JT074084/V1-Bacteria-Killing-Shoe-Display/STL FILES/Door Stuff/V1 FINAL - Door.stl

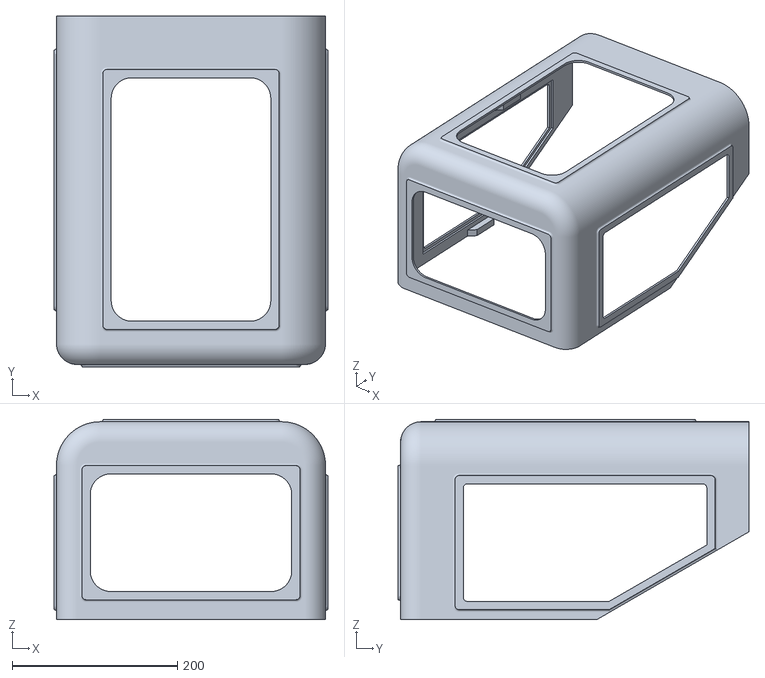
[picture p15: CAD file, 2025-12-03]
STL FILES/Door Stuff/V1 FINAL - Door.stl
331.8 x 425.0 x 242.8
