JT074084/V1-Bacteria-Killing-Shoe-Display/STL FILES/Shoe Bed Stuff/Bed Parts/V1 FINAL - Left Bed - Back.stl

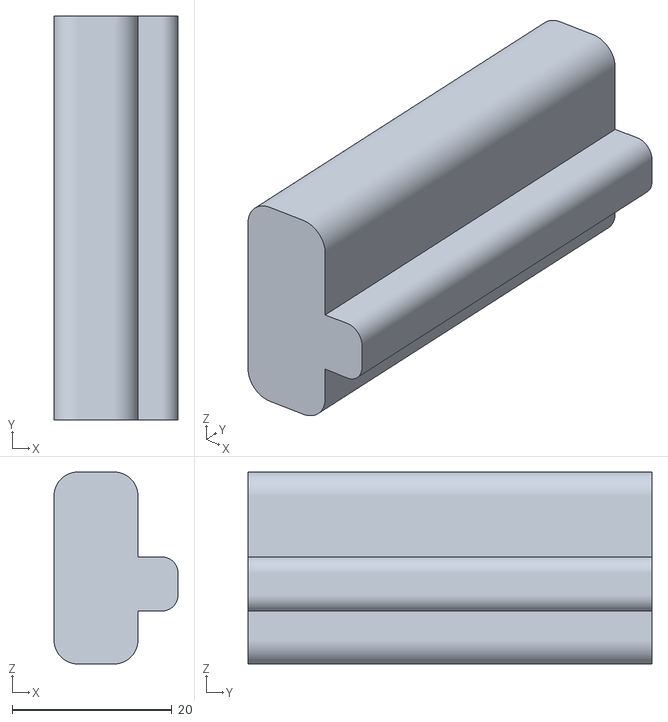
[picture p16: CAD file, 2025-12-03]
STL FILES/Shoe Bed Stuff/Bed Parts/V1 FINAL - Left Bed - Back.stl
15.5 x 50.5 x 24.0
