JT074084/V1-Bacteria-Killing-Shoe-Display/STL FILES/Shoe Bed Stuff/Drag Chain/Wire Chain Bed Connect V1.stl

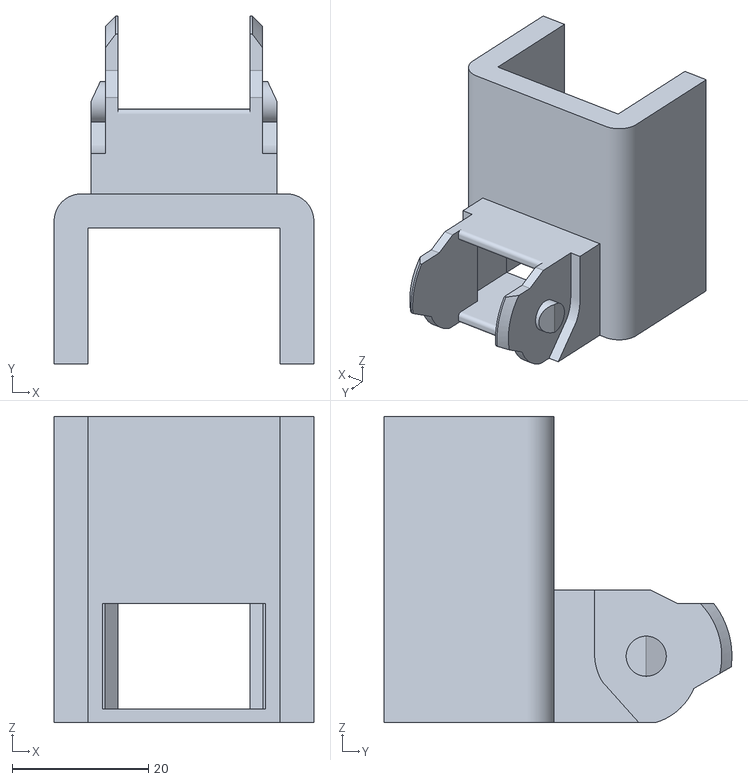
[picture p17: CAD file, 2025-12-03]
STL FILES/Shoe Bed Stuff/Drag Chain/Wire Chain Bed Connect V1.stl
38.2 x 51.1 x 45.0
