JT074084/V1-Bacteria-Killing-Shoe-Display/STL FILES/Shoe Bed Stuff/Logo Cap/V1 FINAL - BPL 2.stl

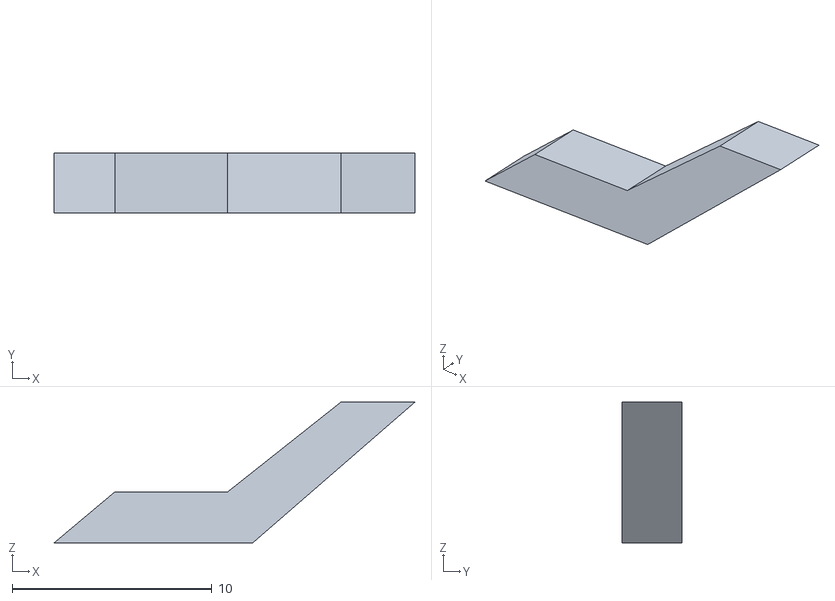
[picture p18: CAD file, 2025-12-03]
STL FILES/Shoe Bed Stuff/Logo Cap/V1 FINAL - BPL 2.stl
18.1 x 3.00 x 7.05
