JT074084/V1-Bacteria-Killing-Shoe-Display/STL FILES/Shoe Bed Stuff/Shoe Sensor and UVC LED Stuff/Shoe Sensor TPU Spring.stl

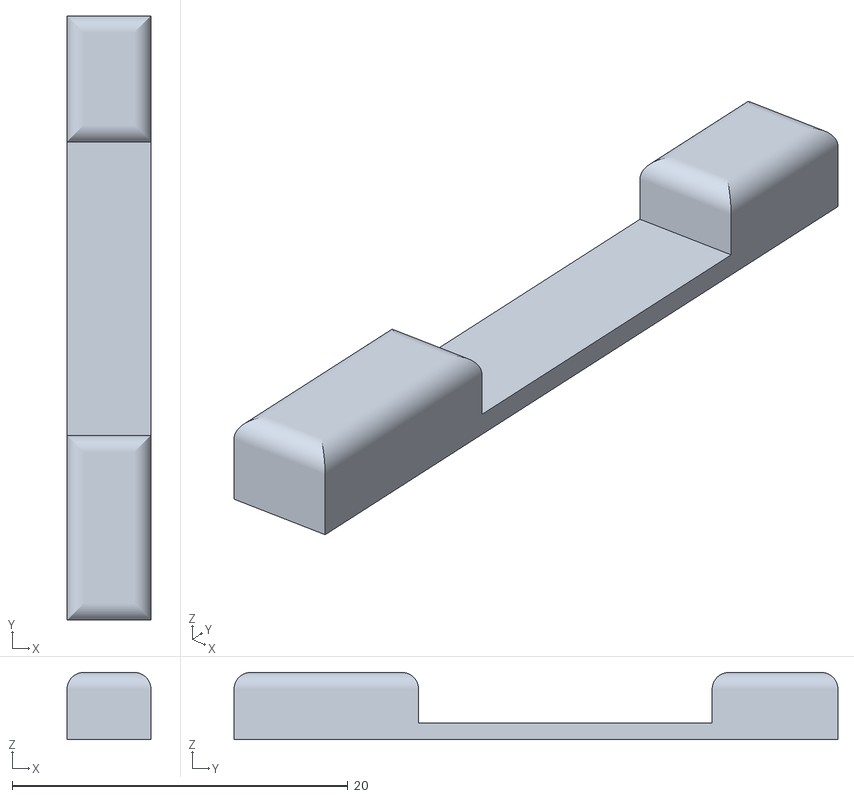
[picture p19: CAD file, 2025-12-03]
STL FILES/Shoe Bed Stuff/Shoe Sensor and UVC LED Stuff/Shoe Sensor TPU Spring.stl
5.00 x 36.0 x 4.00
