JT074084/V1-Bacteria-Killing-Shoe-Display/STL FILES/Shoe Bed Stuff/Shoe Sensor and UVC LED Stuff/UVC LED Stick/UVC LED Stick V1.stl

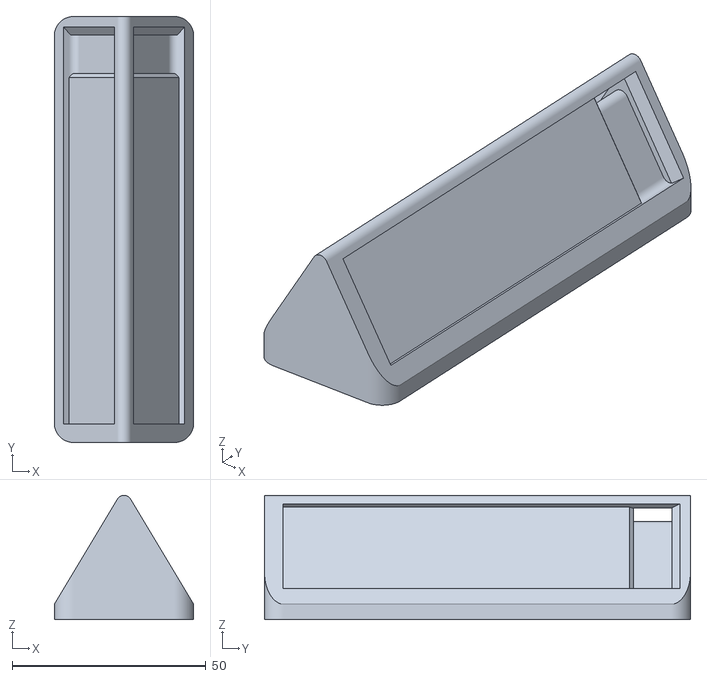
[picture p20: CAD file, 2025-12-03]
STL FILES/Shoe Bed Stuff/Shoe Sensor and UVC LED Stuff/UVC LED Stick/UVC LED Stick V1.stl
36.0 x 110.0 x 32.1
