JT074084/V1-Bacteria-Killing-Shoe-Display/STL FILES/Base Stuff/LED Bar and Base Covers/V1 FINAL - Base Cap.stl

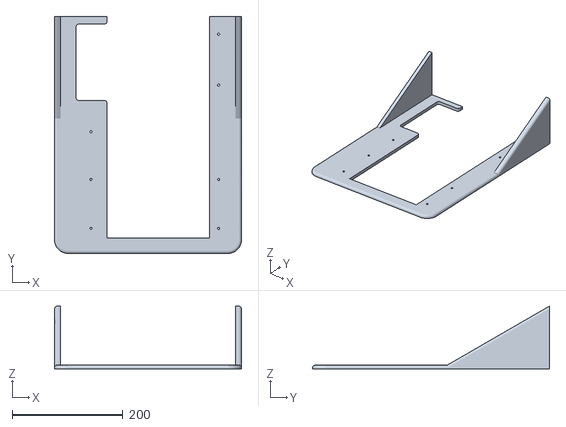
[picture p21: CAD file, 2025-12-03]
STL FILES/Base Stuff/LED Bar and Base Covers/V1 FINAL - Base Cap.stl
337.8 x 428.0 x 113.5
