JT074084/V1-Bacteria-Killing-Shoe-Display/STL FILES/Base Stuff/Left Side Top Half/Left Side Top Half Cap.stl

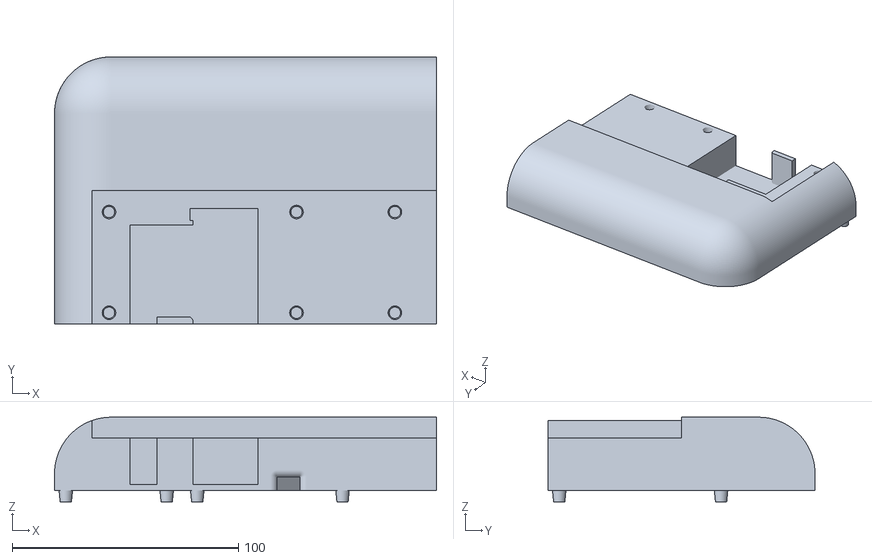
[picture p22: CAD file, 2025-12-03]
STL FILES/Base Stuff/Left Side Top Half/Left Side Top Half Cap.stl
168.9 x 118.1 x 37.4
