JT074084/V1-Bacteria-Killing-Shoe-Display/STL FILES/Base Stuff/Linear Actuator Stuff/Spacers/V1 FINAL - LAS 1.stl

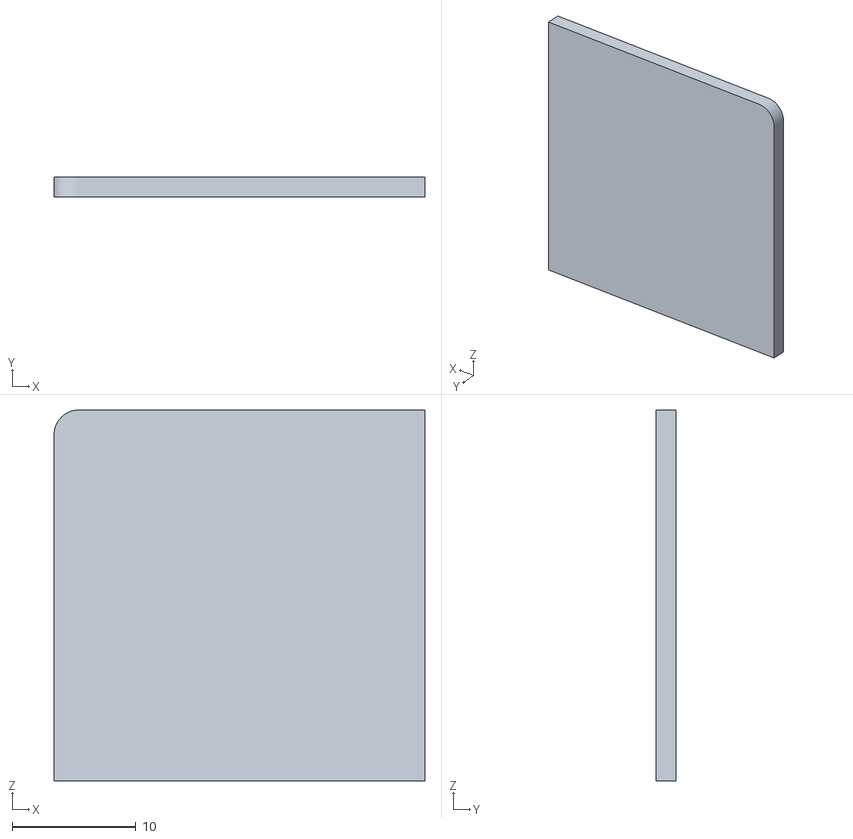
[picture p23: CAD file, 2025-12-03]
STL FILES/Base Stuff/Linear Actuator Stuff/Spacers/V1 FINAL - LAS 1.stl
30.0 x 1.60 x 30.0
