JT074084/V1-Bacteria-Killing-Shoe-Display/STL FILES/Base Stuff/Open:Close Button Stuff/V1 FINAL - Button Spring 2.stl

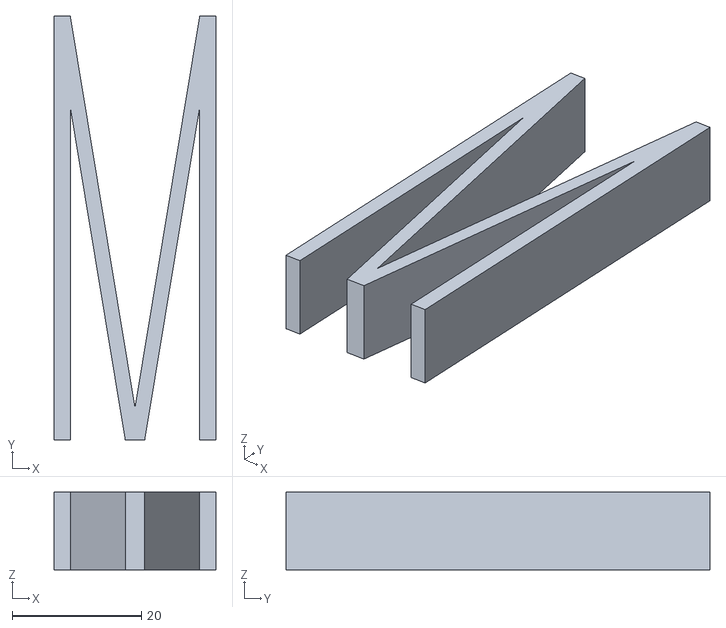
[picture p24: CAD file, 2025-12-03]
STL FILES/Base Stuff/Open:Close Button Stuff/V1 FINAL - Button Spring 2.stl
25.0 x 65.5 x 12.0
