JT074084/V1-Bacteria-Killing-Shoe-Display/STL FILES/Base Stuff/Push Latch Mechanism Side/V1 FINAL - Spring 1.stl

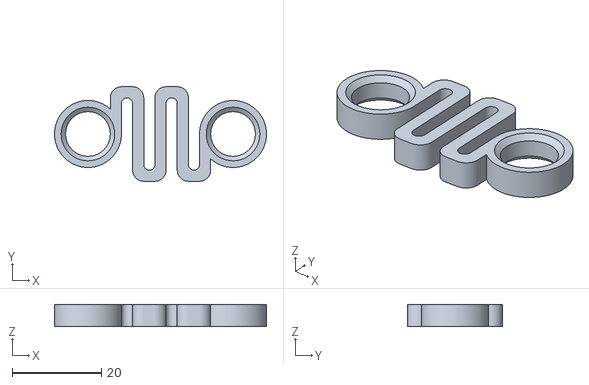
[picture p25: CAD file, 2025-12-03]
STL FILES/Base Stuff/Push Latch Mechanism Side/V1 FINAL - Spring 1.stl
47.5 x 21.2 x 5.00
