JT074084/V1-Bacteria-Killing-Shoe-Display/STL FILES/Base Stuff/Wire Duct Caps/V1 FINAL - Back Wiring Cap 1.stl

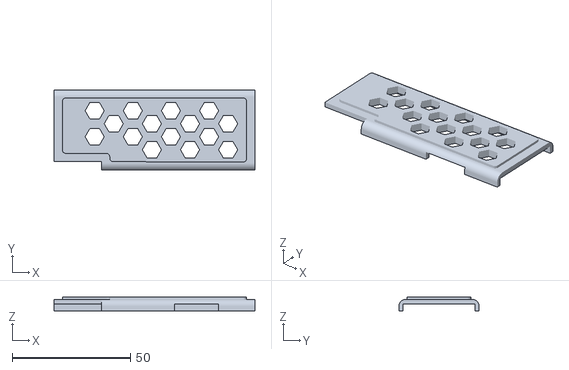
[picture p26: CAD file, 2025-12-03]
STL FILES/Base Stuff/Wire Duct Caps/V1 FINAL - Back Wiring Cap 1.stl
85.0 x 34.0 x 6.00
