JT074084/V1-Bacteria-Killing-Shoe-Display/STL FILES/Door Stuff/Door Arm Stuff/Arm Connecting Pieces/Logo/V1 FINAL - Logo 2.stl

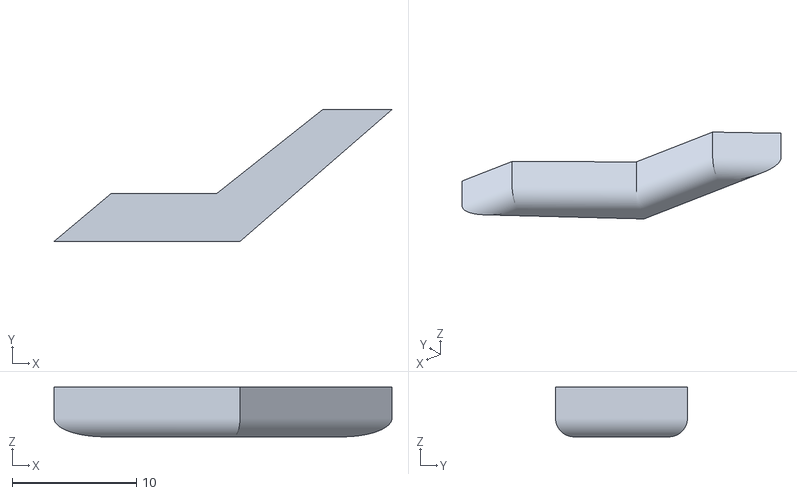
[picture p27: CAD file, 2025-12-03]
STL FILES/Door Stuff/Door Arm Stuff/Arm Connecting Pieces/Logo/V1 FINAL - Logo 2.stl
27.2 x 10.6 x 4.00
