JT074084/V1-Bacteria-Killing-Shoe-Display/STL FILES/Door Stuff/Door Arm Stuff/Arm Connecting Pieces/V1 FINAL - ARM MBB.stl

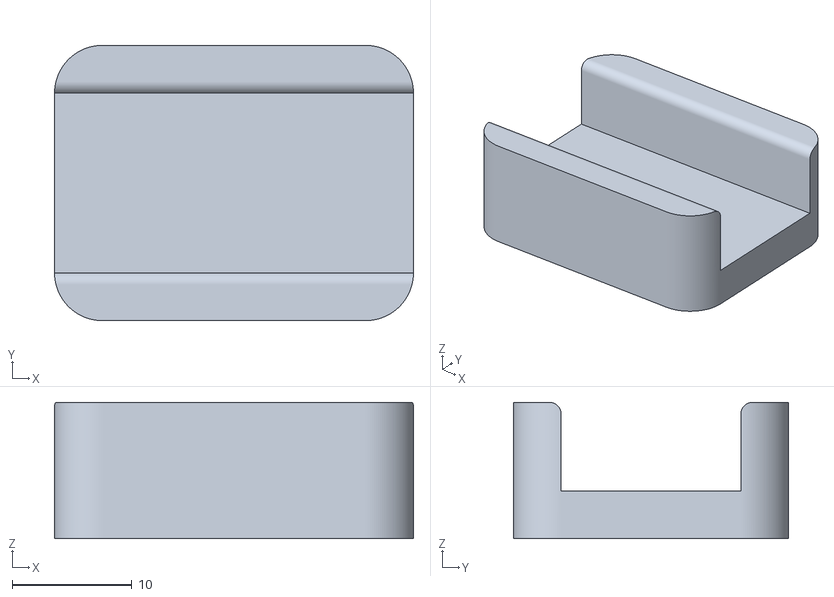
[picture p28: CAD file, 2025-12-03]
STL FILES/Door Stuff/Door Arm Stuff/Arm Connecting Pieces/V1 FINAL - ARM MBB.stl
30.0 x 23.0 x 11.4
