JT074084/V1-Bacteria-Killing-Shoe-Display/STL FILES/Door Stuff/Door Arm Stuff/Right Bearing Case.stl

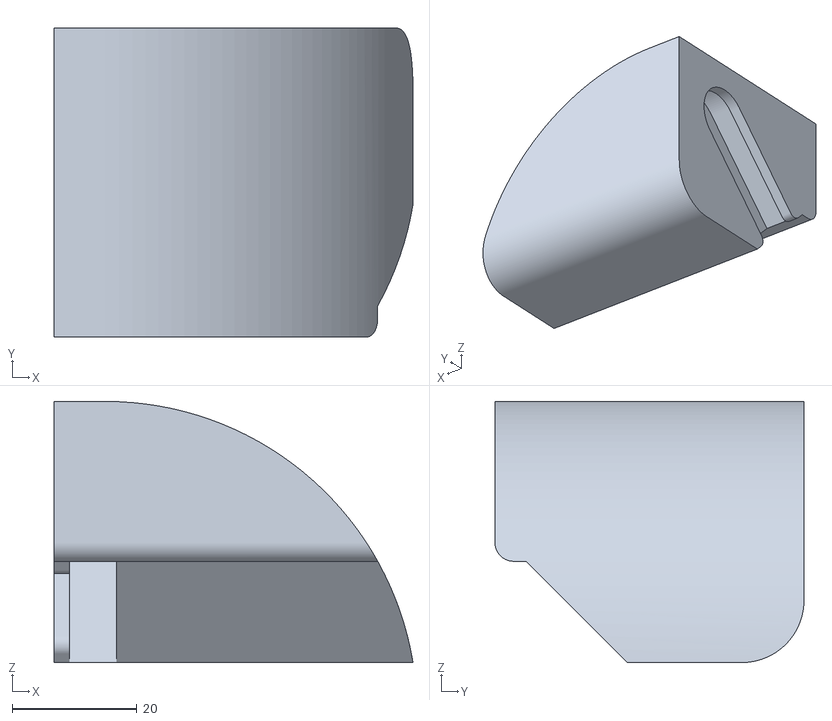
[picture p29: CAD file, 2025-12-03]
STL FILES/Door Stuff/Door Arm Stuff/Right Bearing Case.stl
57.7 x 49.6 x 41.9
