JT074084/V1-Bacteria-Killing-Shoe-Display/STL FILES/Shoe Bed Stuff/Bed Parts/Bed Connect - 2040 Connect.stl

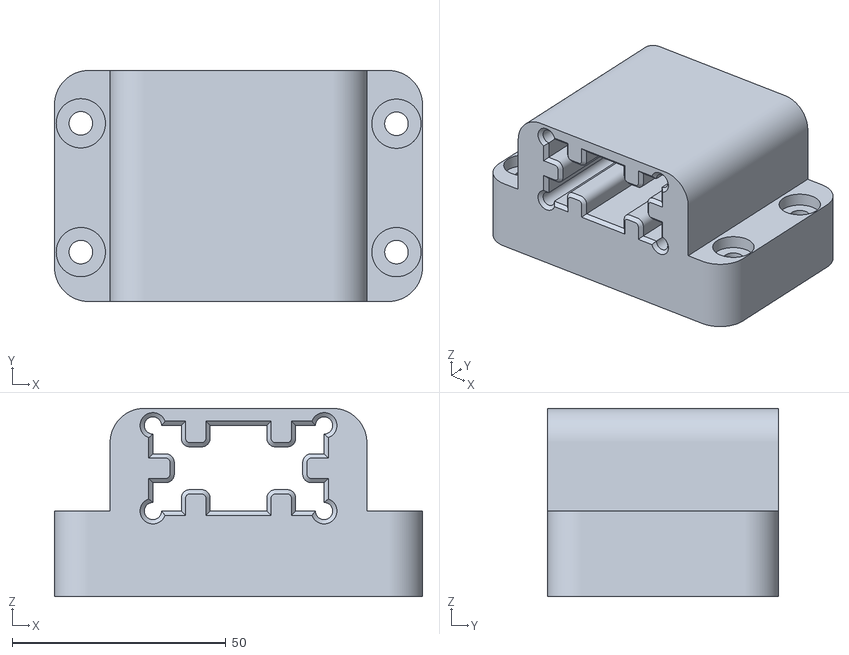
[picture p30: CAD file, 2025-12-03]
STL FILES/Shoe Bed Stuff/Bed Parts/Bed Connect - 2040 Connect.stl
86.0 x 54.0 x 44.0
