JT074084/V1-Bacteria-Killing-Shoe-Display/STL FILES/Shoe Bed Stuff/Drag Chain/chain-segment.stl

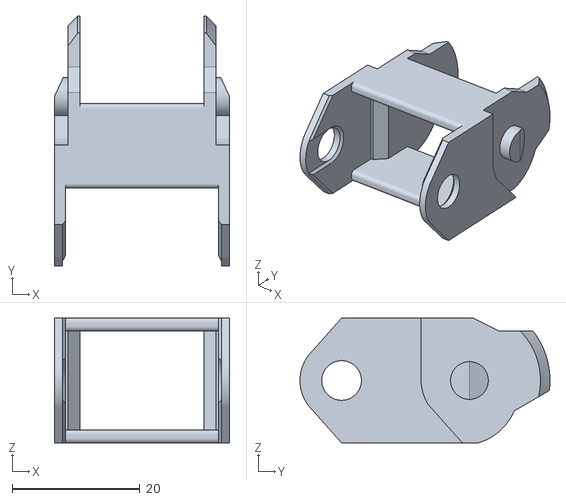
[picture p31: CAD file, 2025-12-03]
STL FILES/Shoe Bed Stuff/Drag Chain/chain-segment.stl
27.4 x 39.1 x 19.5
