JT074084/V1-Bacteria-Killing-Shoe-Display/STL FILES/Shoe Bed Stuff/Logo Cap/V1 FINAL - BPL 3.stl

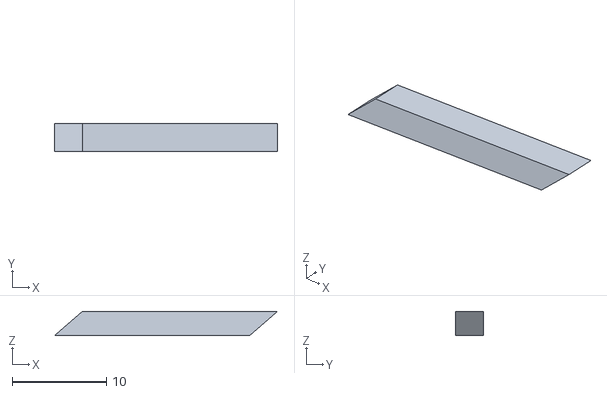
[picture p32: CAD file, 2025-12-03]
STL FILES/Shoe Bed Stuff/Logo Cap/V1 FINAL - BPL 3.stl
23.6 x 3.00 x 2.56
