JT074084/V1-Bacteria-Killing-Shoe-Display/STL FILES/Shoe Bed Stuff/Shoe Sensor and UVC LED Stuff/V1 FINAL - Shoe Sensor.stl

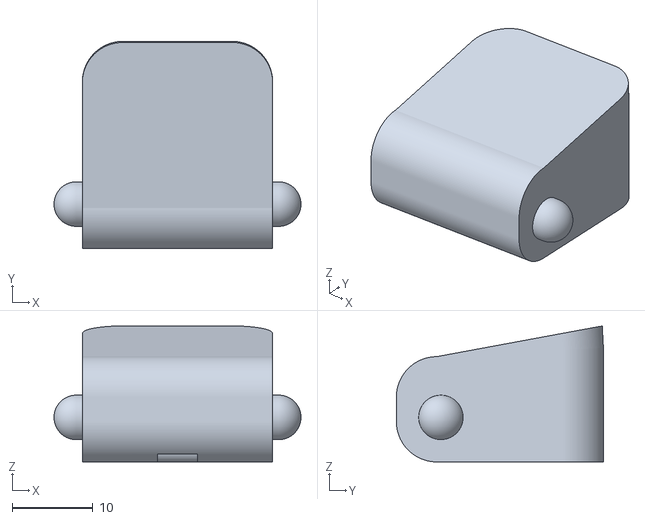
[picture p33: CAD file, 2025-12-03]
STL FILES/Shoe Bed Stuff/Shoe Sensor and UVC LED Stuff/V1 FINAL - Shoe Sensor.stl
30.5 x 25.6 x 16.8
