JT074084/V1-Bacteria-Killing-Shoe-Display/STL FILES/Base Stuff/LED Bar and Base Covers/V1 FINAL - Side LED Attachment.stl

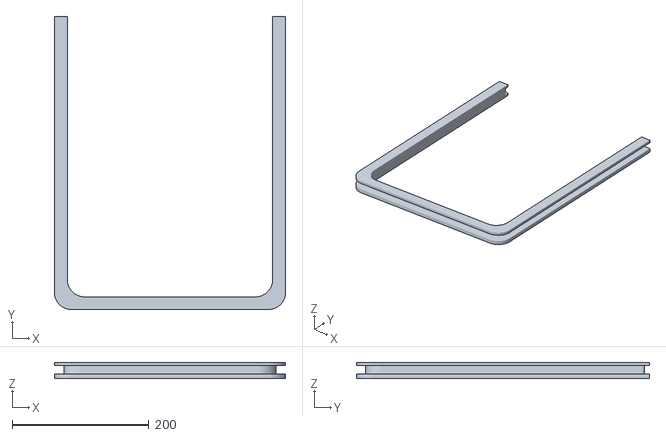
[picture p34: CAD file, 2025-12-03]
STL FILES/Base Stuff/LED Bar and Base Covers/V1 FINAL - Side LED Attachment.stl
337.8 x 428.0 x 24.0
