JT074084/V1-Bacteria-Killing-Shoe-Display/STL FILES/Base Stuff/Left Side Top Half/Servo Area Cap.stl

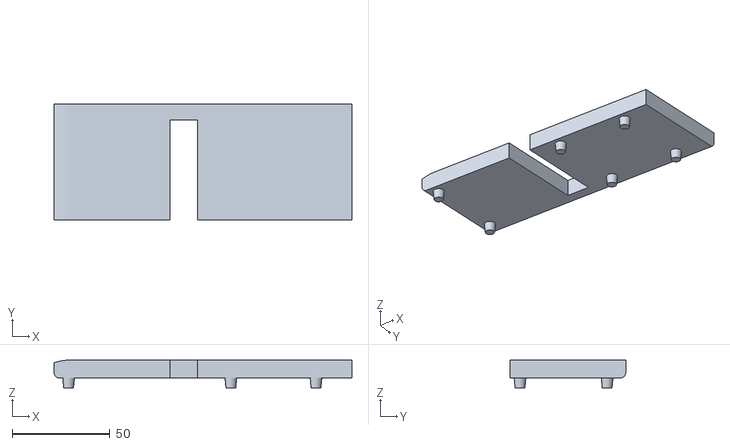
[picture p35: CAD file, 2025-12-03]
STL FILES/Base Stuff/Left Side Top Half/Servo Area Cap.stl
152.3 x 59.1 x 14.3
