JT074084/V1-Bacteria-Killing-Shoe-Display/STL FILES/Base Stuff/Open:Close Button Stuff/V1 FINAL - Open-Close Button.stl

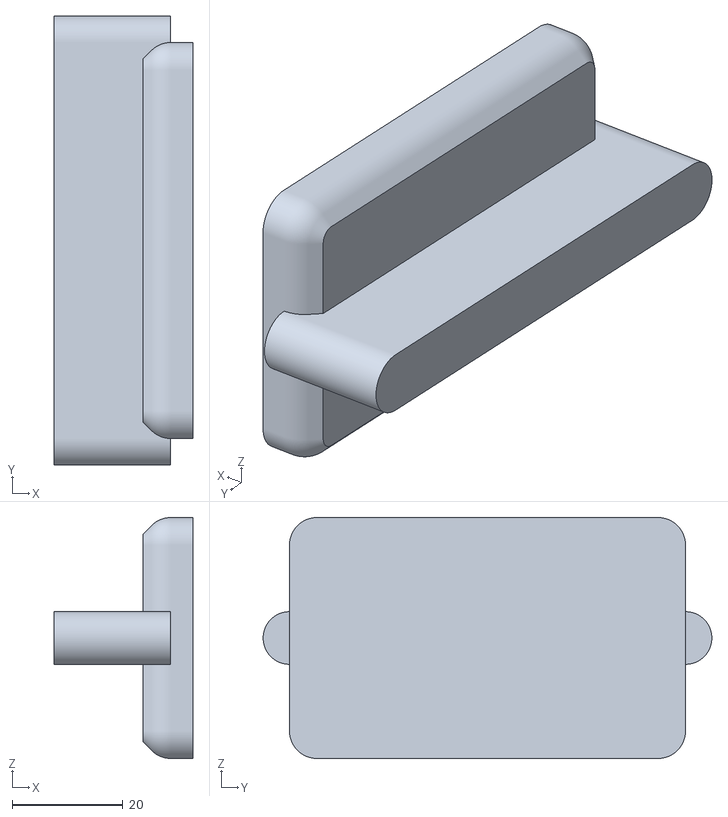
[picture p36: CAD file, 2025-12-03]
STL FILES/Base Stuff/Open:Close Button Stuff/V1 FINAL - Open-Close Button.stl
25.0 x 81.0 x 43.5
