JT074084/V1-Bacteria-Killing-Shoe-Display/STL FILES/Base Stuff/Push Latch Mechanism Side/Arm Bearing Cap.stl

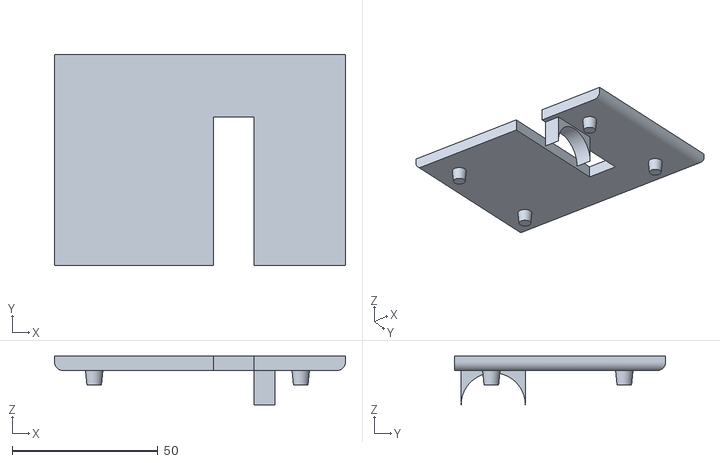
[picture p37: CAD file, 2025-12-03]
STL FILES/Base Stuff/Push Latch Mechanism Side/Arm Bearing Cap.stl
99.8 x 72.5 x 16.8
