JT074084/V1-Bacteria-Killing-Shoe-Display/STL FILES/Base Stuff/Wire Duct Caps/V1 FINAL - Back Wiring Cap 3.stl

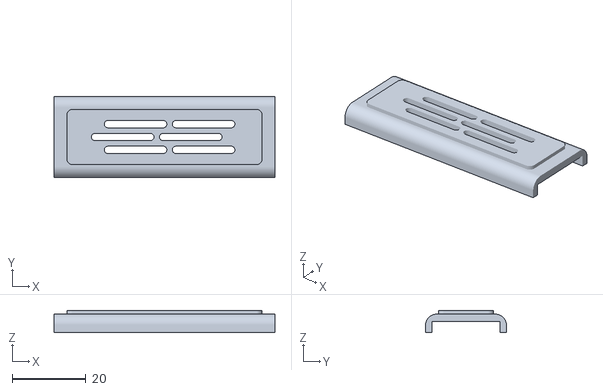
[picture p38: CAD file, 2025-12-03]
STL FILES/Base Stuff/Wire Duct Caps/V1 FINAL - Back Wiring Cap 3.stl
60.1 x 22.0 x 6.00
