JT074084/V1-Bacteria-Killing-Shoe-Display/STL FILES/Door Stuff/Door Arm Stuff/Arm Connecting Pieces/Logo/V1 FINAL - Logo 3.stl

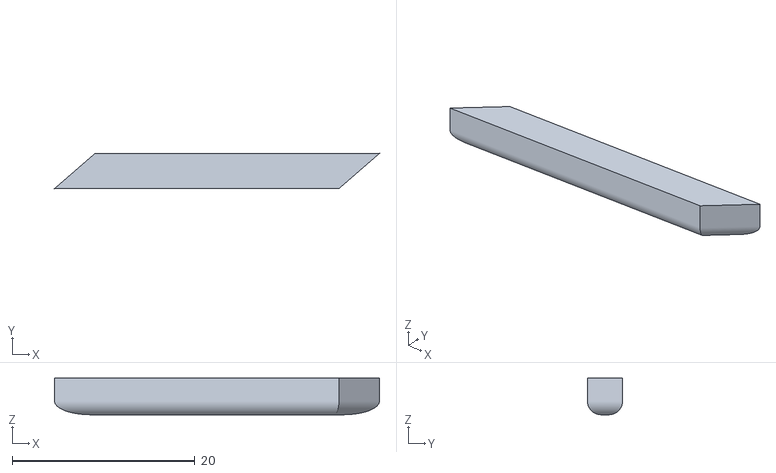
[picture p39: CAD file, 2025-12-03]
STL FILES/Door Stuff/Door Arm Stuff/Arm Connecting Pieces/Logo/V1 FINAL - Logo 3.stl
35.6 x 3.85 x 4.00
