JT074084/V1-Bacteria-Killing-Shoe-Display/STL FILES/Shoe Bed Stuff/Shoe Sensor and UVC LED Stuff/V1 FINAL - Wire Canal Cap.stl

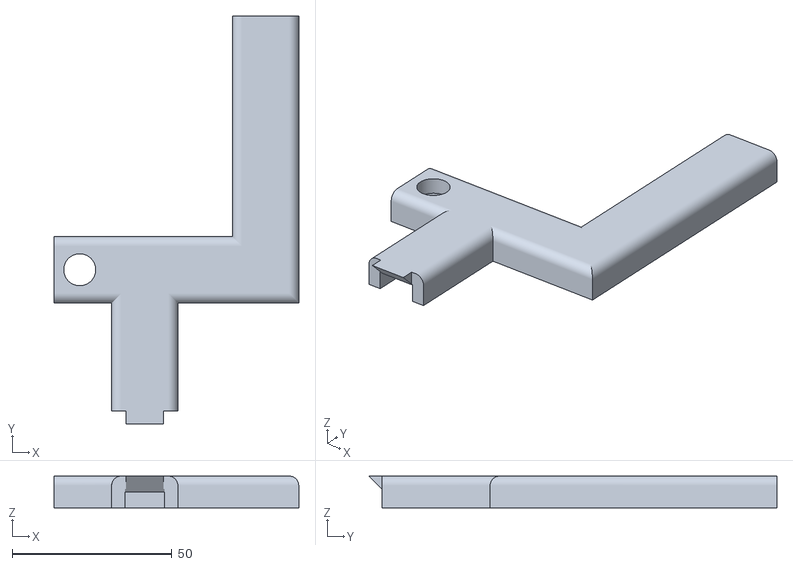
[picture p41: CAD file, 2025-12-03]
STL FILES/Shoe Bed Stuff/Shoe Sensor and UVC LED Stuff/V1 FINAL - Wire Canal Cap.stl
76.7 x 127.9 x 10.0
