JT074084/V1-Bacteria-Killing-Shoe-Display/STL FILES/Base Stuff/Left Side Top Half/Left Side Top Half Inside Fan Guard.stl

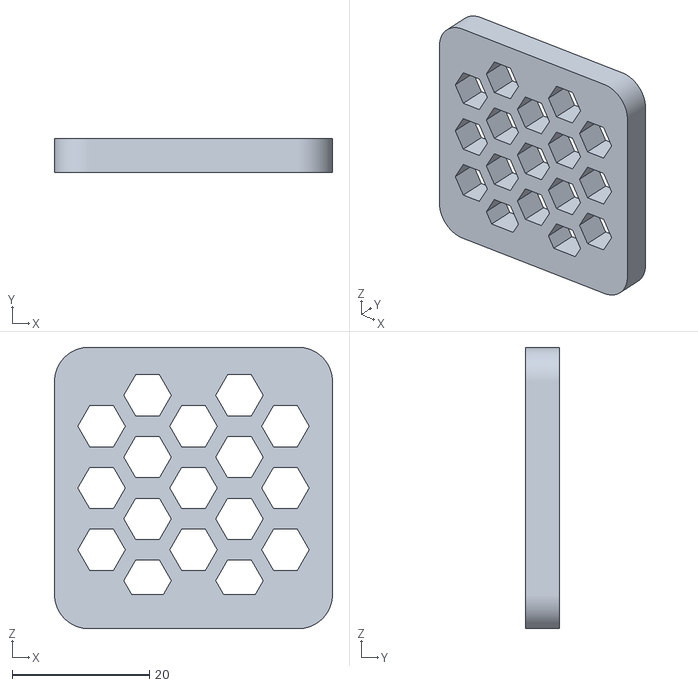
[picture p42: CAD file, 2025-12-03]
STL FILES/Base Stuff/Left Side Top Half/Left Side Top Half Inside Fan Guard.stl
40.5 x 5.00 x 41.0
