JT074084/V1-Bacteria-Killing-Shoe-Display/STL FILES/Base Stuff/Linear Actuator Stuff/Spacers/V1 FINAL - LAS 4.stl

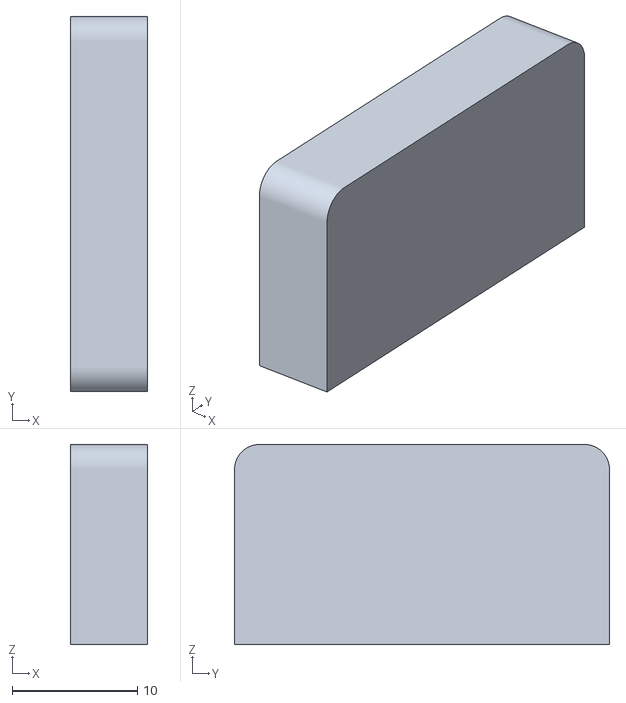
[picture p43: CAD file, 2025-12-03]
STL FILES/Base Stuff/Linear Actuator Stuff/Spacers/V1 FINAL - LAS 4.stl
6.15 x 30.0 x 16.0
