JT074084/V1-Bacteria-Killing-Shoe-Display/STL FILES/Base Stuff/Push Latch Mechanism Side/PLM Inside Fan Guard.stl

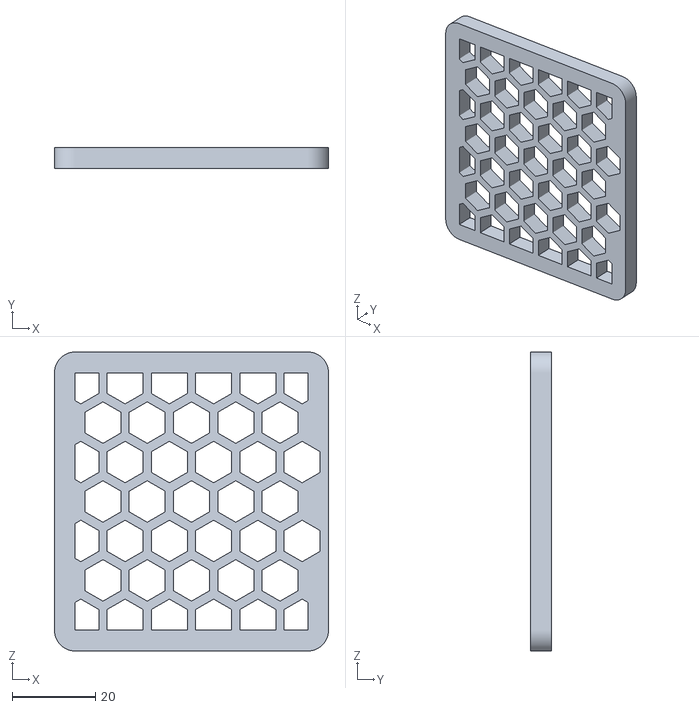
[picture p44: CAD file, 2025-12-03]
STL FILES/Base Stuff/Push Latch Mechanism Side/PLM Inside Fan Guard.stl
66.0 x 5.00 x 72.0
