JT074084/V1-Bacteria-Killing-Shoe-Display/STL FILES/Base Stuff/Wire Duct Caps/V1 FINAL - Left Wiring Cap.stl

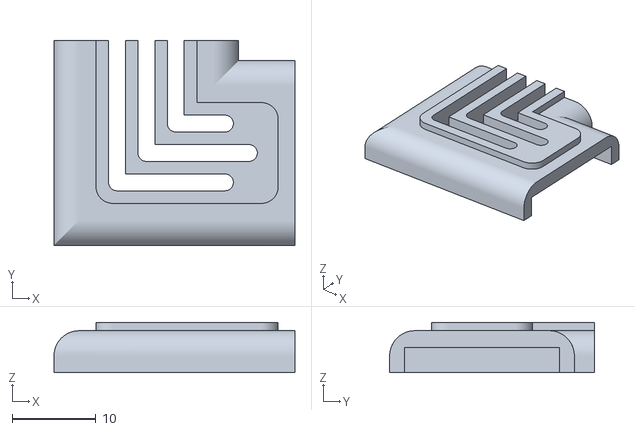
[picture p45: CAD file, 2025-12-03]
STL FILES/Base Stuff/Wire Duct Caps/V1 FINAL - Left Wiring Cap.stl
28.7 x 24.4 x 6.00
