JT074084/V1-Bacteria-Killing-Shoe-Display/STL FILES/Door Stuff/Door Arm Stuff/Door Arm.stl

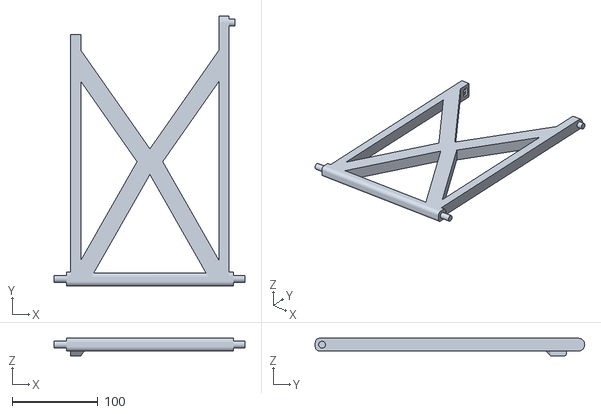
[picture p47: CAD file, 2025-12-03]
STL FILES/Door Stuff/Door Arm Stuff/Door Arm.stl
223.2 x 315.0 x 20.5
