JT074084/V1-Bacteria-Killing-Shoe-Display/STL FILES/Base Stuff/Linear Actuator Stuff/Spacers/V1 FINAL - LAS2.stl

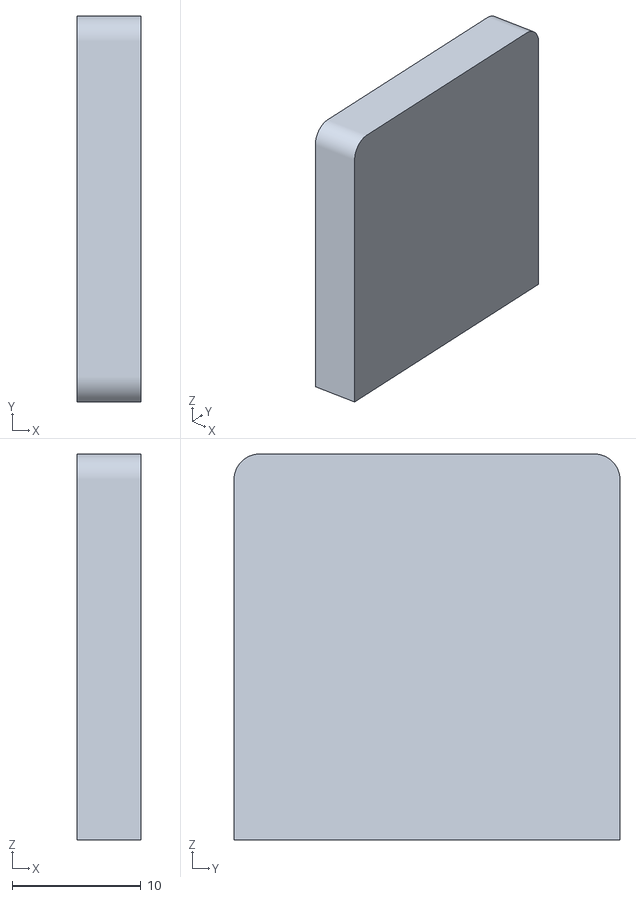
[picture p49: CAD file, 2025-12-03]
STL FILES/Base Stuff/Linear Actuator Stuff/Spacers/V1 FINAL - LAS2.stl
5.00 x 30.0 x 30.0
