JT074084/V1-Bacteria-Killing-Shoe-Display/STL FILES/Base Stuff/Push Latch Mechanism Side/PLM Chlorine Dioxide Cartridge.stl

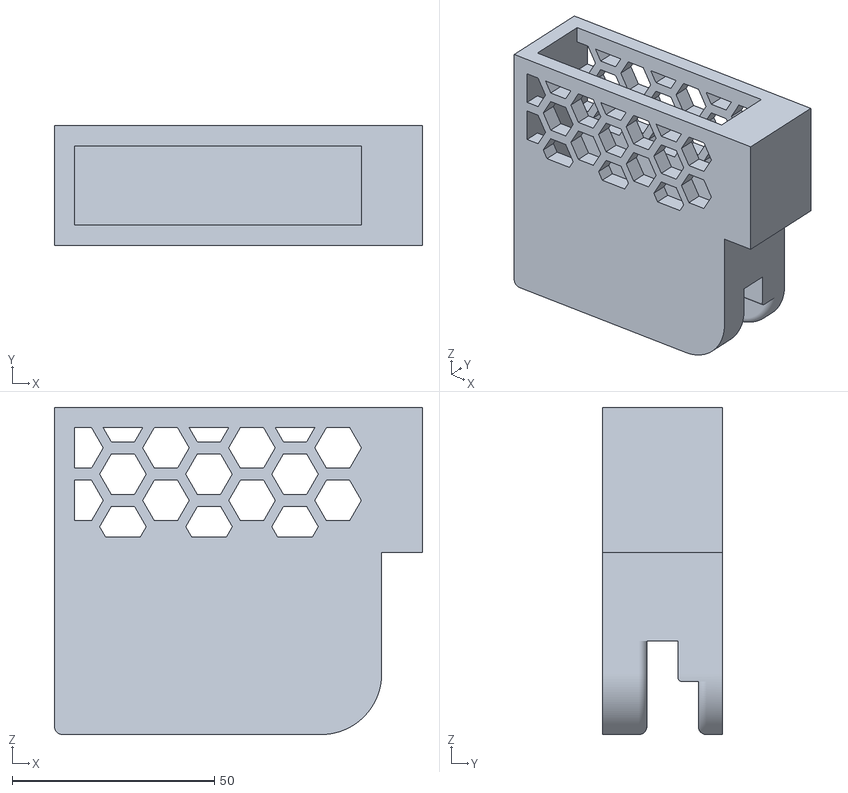
[picture p50: CAD file, 2025-12-03]
STL FILES/Base Stuff/Push Latch Mechanism Side/PLM Chlorine Dioxide Cartridge.stl
91.0 x 29.6 x 80.9
