JT074084/V1-Bacteria-Killing-Shoe-Display/STL FILES/Base Stuff/Wire Duct Caps/V1 FINAL - Right Wiring Cap.stl

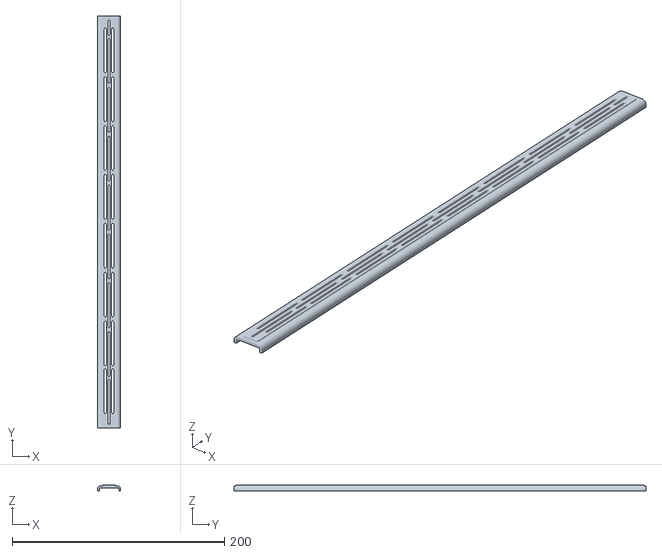
[picture p51: CAD file, 2025-12-03]
STL FILES/Base Stuff/Wire Duct Caps/V1 FINAL - Right Wiring Cap.stl
21.8 x 388.0 x 6.00
