JT074084/V1-Bacteria-Killing-Shoe-Display/STL FILES/Door Stuff/Door Arm Stuff/Arm Connecting Pieces/V1 FINAL - ARM MB.stl

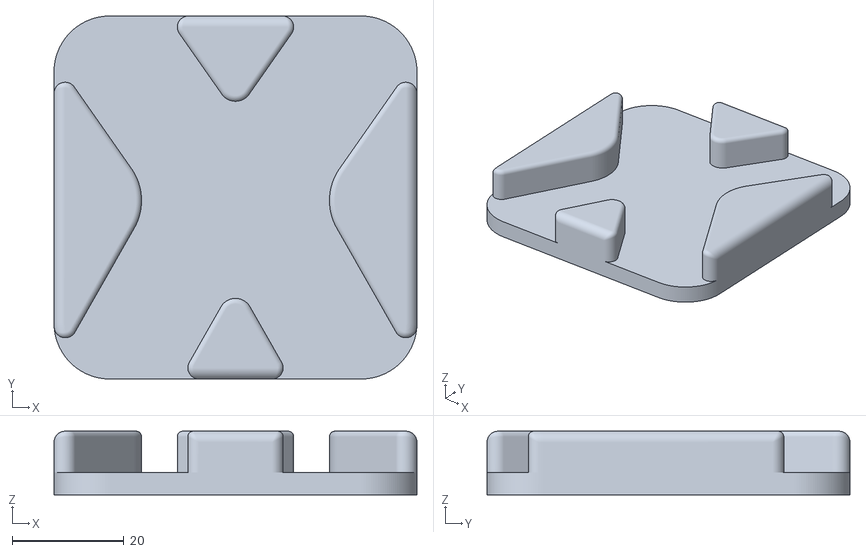
[picture p52: CAD file, 2025-12-03]
STL FILES/Door Stuff/Door Arm Stuff/Arm Connecting Pieces/V1 FINAL - ARM MB.stl
65.0 x 65.0 x 11.4
