JT074084/V1-Bacteria-Killing-Shoe-Display/STL FILES/Shoe Bed Stuff/Logo Cap/V1 FINAL - Metal Bar Cap.stl

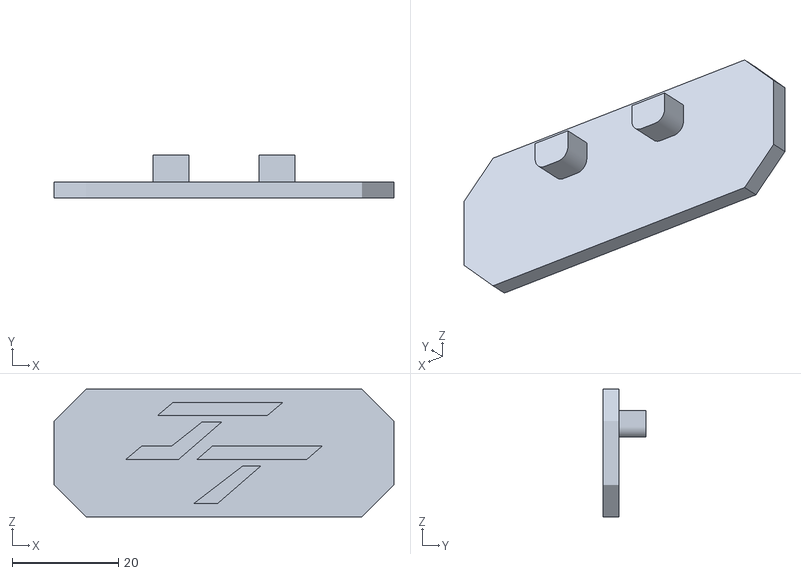
[picture p53: CAD file, 2025-12-03]
STL FILES/Shoe Bed Stuff/Logo Cap/V1 FINAL - Metal Bar Cap.stl
64.0 x 8.00 x 24.0
