JT074084/V1-Bacteria-Killing-Shoe-Display/STL FILES/Base Stuff/Left Side Top Half/Left Side Top Half Outside Fan Guard.stl

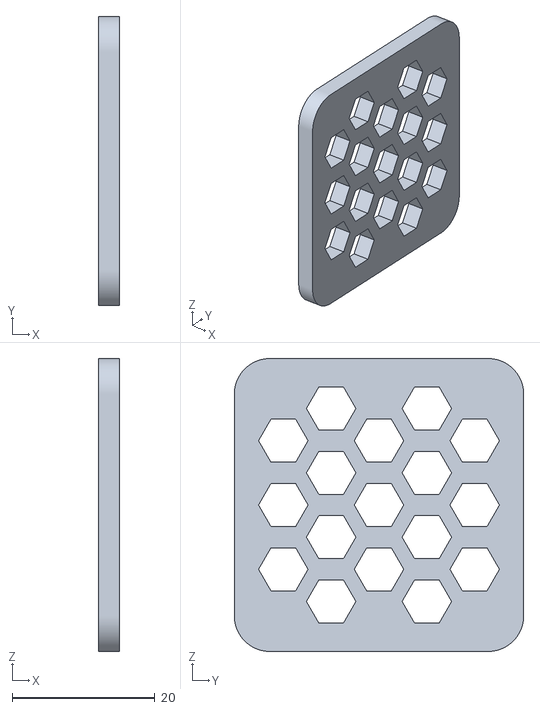
[picture p54: CAD file, 2025-12-03]
STL FILES/Base Stuff/Left Side Top Half/Left Side Top Half Outside Fan Guard.stl
3.00 x 40.5 x 41.0
