JT074084/V1-Bacteria-Killing-Shoe-Display/STL FILES/Base Stuff/Linear Actuator Stuff/Spacers/V1 FINAL - LAS3.stl

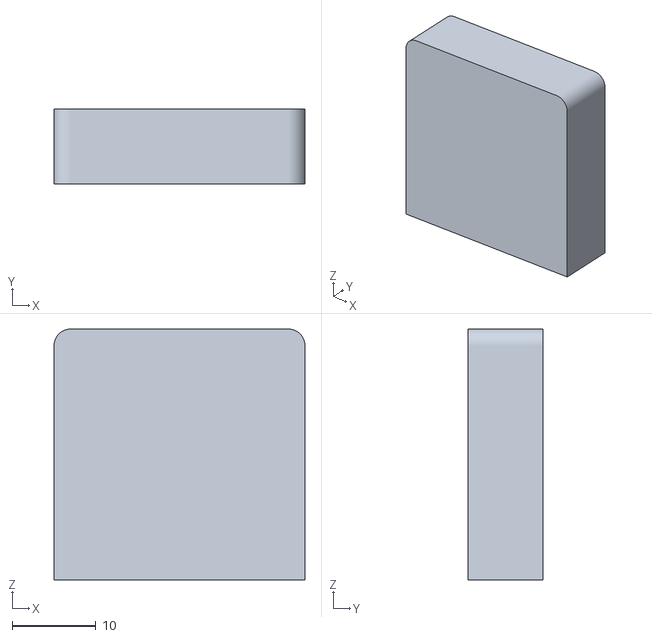
[picture p55: CAD file, 2025-12-03]
STL FILES/Base Stuff/Linear Actuator Stuff/Spacers/V1 FINAL - LAS3.stl
30.0 x 9.00 x 30.0
