JT074084/V1-Bacteria-Killing-Shoe-Display/STL FILES/Base Stuff/Push Latch Mechanism Side/PLM Outside Fan Guard.stl

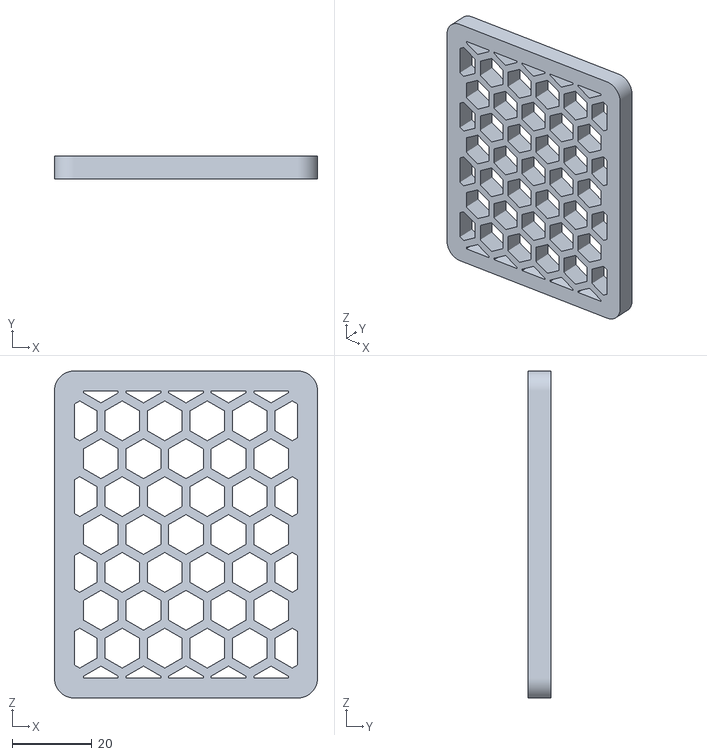
[picture p56: CAD file, 2025-12-03]
STL FILES/Base Stuff/Push Latch Mechanism Side/PLM Outside Fan Guard.stl
66.0 x 5.82 x 82.0
