JT074084/V1-Bacteria-Killing-Shoe-Display/STL FILES/Base Stuff/Wire Duct Caps/V1 FINAL - Back Wiring Cap 2.stl

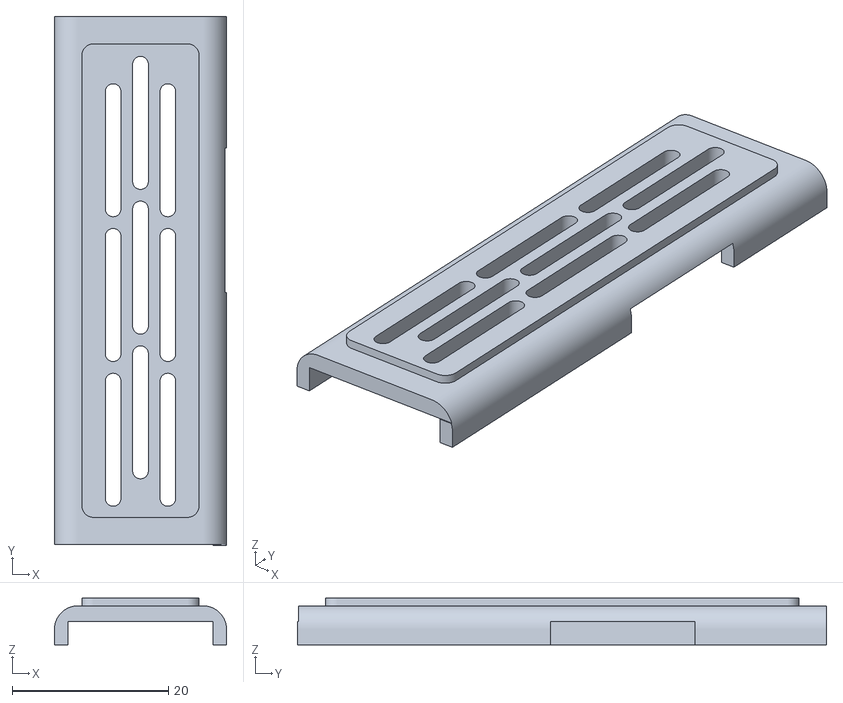
[picture p57: CAD file, 2025-12-03]
STL FILES/Base Stuff/Wire Duct Caps/V1 FINAL - Back Wiring Cap 2.stl
22.0 x 67.6 x 6.00
