JT074084/V1-Bacteria-Killing-Shoe-Display/STL FILES/Base Stuff/Push Latch Mechanism Side/PLM Base.stl

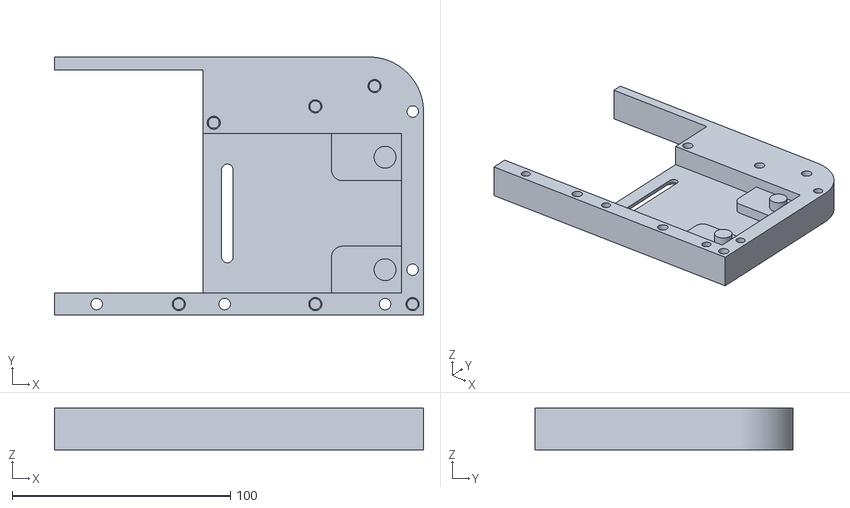
[picture p58: CAD file, 2025-12-03]
STL FILES/Base Stuff/Push Latch Mechanism Side/PLM Base.stl
168.9 x 118.1 x 19.0
