JT074084/V1-Bacteria-Killing-Shoe-Display/STL FILES/Base Stuff/Push Latch Mechanism Side/PLM Slider Peg Cap.stl

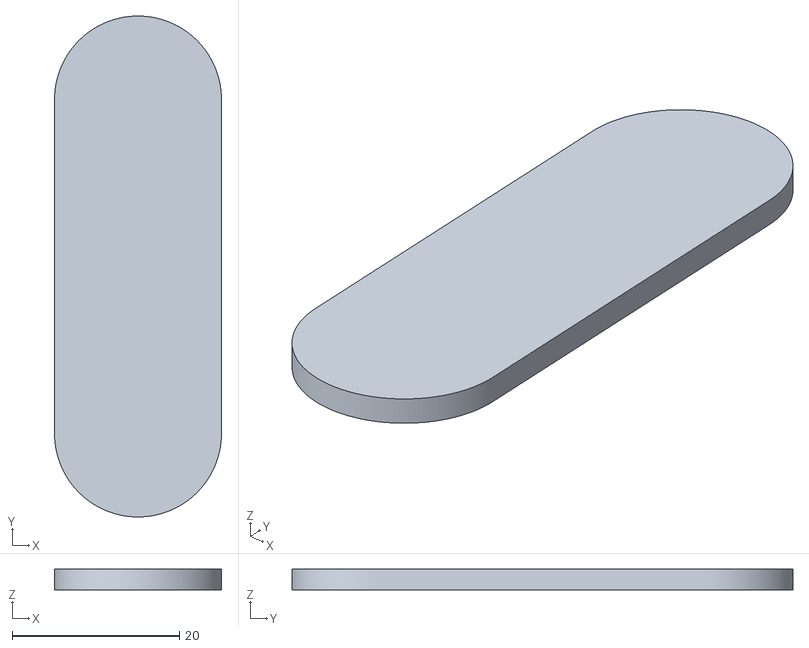
[picture p60: CAD file, 2025-12-03]
STL FILES/Base Stuff/Push Latch Mechanism Side/PLM Slider Peg Cap.stl
20.0 x 60.0 x 2.50
